westonb/rogowski-relief/sim/amp_sim_freq.asc

C1: cap; 47p
C2: cap; 15p
C21: cap; 7p
C23: cap; 200p
C24: cap; 330p
C26: cap; 47n
C28: cap; 10p
C30: cap; 6p
I2: current; AC 1
L7: ind; 8.5n; Rser=0
L8: ind; 4.7µ
R1: res; 169
R2: res; {200*(1-G_ADJ)}
R3: res; {200*(G_ADJ)}
R4: res; 220
R5: res; 1.2k
R6: res; 10k
R7: res; 470
R13: res; 430
R14: res; {200*C_ADJ}
R16: res; 680
R39: res; 47
R43: res; 22k
R44: res; 22k
R45: res; 22k
R46: res; 22k
R48: res; 220
R51: res; 8k
R52: res; 1Meg
R53: res; 47
T5: tline; Td=2.2n Z0=50
T6: tline; Td=3n Z0=50
U9: UniversalOpamp2; Avol=316k GBW=40Meg Slew=10Meg
U10: UniversalOpamp2; Avol=316k GBW=130Meg Slew=100Meg; ilimit=80m rail=0 Vos=0 phimargin=45
U11: UniversalOpamp2; Avol=316k GBW=130Meg Slew=100Meg; ilimit=80m rail=0 Vos=0 phimargin=45
V1: voltage; 6
V2: voltage; 6
Named nets: 0, VP, VN, coil_out, OUT_INT, OUT
.ac oct 1k 100 50Meg
18" of cable
coil termination resistor
passive integrating capacitor
~25pF
models DM impedance of OPA
3' of cable
~100pF
Peaking to compensate for coil loss
Requires loss model for coil to accurately sim
Scope Load
.param G_ADJ 0.27
.param C_ADJ 0.6
OPA2822
OPA2822
TLV2172
rogowski coil
