westonb/rogowski-relief/sim/amp_sim_transient.asc

C1: cap; 7p
C2: cap; 200p
C3: cap; 330p
C4: cap; 47n
C5: cap; 10p
C6: cap; 6p
C7: cap; 47p
C8: cap; 15p
I1: current; PULSE(-1 1 0 50n 50n 1u 2u); AC 1
L1: ind; 8.5n; Rser=0
L2: ind; 4.7µ
R1: res; 680
R2: res; 47
R3: res; 22k
R4: res; 22k
R5: res; 22k
R6: res; 22k
R7: res; 220
R8: res; 8k
R9: res; 1Meg
R10: res; 47
R11: res; 169
R12: res; {200*(1-G_ADJ)}
R13: res; {200*(G_ADJ)}
R14: res; 220
R15: res; 1.2k
R16: res; 10k
R17: res; 470
R18: res; 430
R19: res; {200*C_ADJ}
T1: tline; Td=2.2n Z0=50
T2: tline; Td=3n Z0=50
U1: UniversalOpamp2; Avol=316k GBW=40Meg Slew=10Meg
U2: UniversalOpamp2; Avol=316k GBW=130Meg Slew=100Meg; ilimit=80m rail=0 Vos=0 phimargin=45
U3: UniversalOpamp2; Avol=316k GBW=130Meg Slew=100Meg; ilimit=80m rail=0 Vos=0 phimargin=45
V3: voltage; 6
V4: voltage; 6
Named nets: 0, VP, VN, coil_out, OUT_INT, OUT
.tran 25u
18" of cable
coil termination resistor
passive integrating capacitor
~25pF
models DM impedance of OPA
3' of cable
~100pF
Peaking to compensate for coil loss
Requires loss model for coil to accurately sim
Scope Load
.param G_ADJ 0.27
.param C_ADJ 0.6
OPA2822
OPA2822
TLV2172
rogowski coil
